XerophilousY/STM32-DIY-SYNTH/firmware/Hardware/led.c

#include "led.h"


//LED IO初始化
void LED_Init(void)
{
	 GPIO_InitTypeDef  GPIO_InitStructure;
	 RCC_APB2PeriphClockCmd(RCC_APB2Periph_GPIOC, ENABLE);	 //使能PB,PC端口时钟
	 GPIO_InitStructure.GPIO_Pin = GPIO_Pin_13;		 
	 GPIO_InitStructure.GPIO_Mode = GPIO_Mode_Out_PP; 		 //推挽输出
	 GPIO_InitStructure.GPIO_Speed = GPIO_Speed_50MHz;		 //IO口速度为50MHz
	 GPIO_Init(GPIOC, &GPIO_InitStructure);
	
	 RCC_APB2PeriphClockCmd(RCC_APB2Periph_GPIOB, ENABLE);	 //使能PB端口时钟
	 GPIO_InitStructure.GPIO_Pin = GPIO_Pin_11;		 
 
	 GPIO_Init(GPIOB, &GPIO_InitStructure);	 
	
	 RCC_APB2PeriphClockCmd(RCC_APB2Periph_GPIOA, ENABLE);	 //使能PA端口时钟
	 GPIO_InitStructure.GPIO_Pin = GPIO_Pin_1;		 
	 GPIO_InitStructure.GPIO_Mode = GPIO_Mode_IPU; 		 
	 GPIO_Init(GPIOA, &GPIO_InitStructure);
	
	 RCC_APB2PeriphClockCmd(RCC_APB2Periph_GPIOB, ENABLE);	 //使能PB端口时钟
	 GPIO_InitStructure.GPIO_Pin = GPIO_Pin_5;		 
	 GPIO_InitStructure.GPIO_Mode = GPIO_Mode_IN_FLOATING; 		 
	 GPIO_Init(GPIOB, &GPIO_InitStructure);	 
	
	 //BEEP
	 RCC_APB2PeriphClockCmd(RCC_APB2Periph_GPIOB, ENABLE);	 //使能PA端口时钟
	 GPIO_InitStructure.GPIO_Pin = GPIO_Pin_6;		 
	 GPIO_InitStructure.GPIO_Mode = GPIO_Mode_Out_PP; 		 
	 GPIO_InitStructure.GPIO_Speed = GPIO_Speed_50MHz;		 //IO口速度为50MHz
	 GPIO_Init(GPIOB, &GPIO_InitStructure);
}
 
